dea82/FridgeAlarm/src/cont.c

/*
The MIT License (MIT)

Copyright (c) 2015-2016 Andreas L.

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
THE SOFTWARE IS PROVIDED "AS IS", WITHOUT WARRANTY OF ANY KIND, EXPRESS OR
IMPLIED, INCLUDING BUT NOT LIMITED TO THE WARRANTIES OF MERCHANTABILITY,
FITNESS FOR A PARTICULAR PURPOSE AND NONINFRINGEMENT. IN NO EVENT SHALL THE
AUTHORS OR COPYRIGHT HOLDERS BE LIABLE FOR ANY CLAIM, DAMAGES OR OTHER
LIABILITY, WHETHER IN AN ACTION OF CONTRACT, TORT OR OTHERWISE, ARISING FROM,
OUT OF OR IN CONNECTION WITH THE SOFTWARE OR THE USE OR OTHER DEALINGS IN
THE SOFTWARE.
*/

/**
 * @file
 */

#include "cont.h"

#include "butt.h"
#include "buzz.h"
#include "conf.h"
#include "ledc.h"
#include "door.h"
#include "pwrd.h"
#include "util.h"


typedef enum
{
    NO_CALIBRATION_E, CALIBRATION_SUCCESS_E, CALIBRATION_FAIL_E
} tCalibrationState_E;

static tCalibrationState_E getCalibrationState_E(void);
static void normalModeStateMachine(void);

void Cont_Init(void)
{
    /* Nothing */
}

void Cont_Loop(void)
{
    tCalibrationState_E calibrationState_E = getCalibrationState_E();

    /* Sets it default. */
    Pwrd_SetSleepMode(PWRD_SHORT_DEEP_SLEEP_E);

    if (calibrationState_E == CALIBRATION_SUCCESS_E)
    {
        Buzz_SetSound(BUZZ_OFF_E);
        Ledc_SetState(LEDC_GREEN_BLINK_E);
    }
    else if (calibrationState_E == CALIBRATION_FAIL_E)
    {
        Buzz_SetSound(BUZZ_ON_E);
        Ledc_SetState(LEDC_RED_BLINK_E);
        Pwrd_SetSleepMode(PWRD_SLEEP_WITH_TIMER_RUNNING_E);
    }
    else
    {
        normalModeStateMachine();
    }
}

static tCalibrationState_E getCalibrationState_E(void)
{
    static tCalibrationState_E calibrationState_E;
    tButt_State_str buttState_str = Butt_GetState_str();

    /* Calibration state */
    if ((buttState_str.state_E == BUTT_PRESSED_E) &&
        (buttState_str.tickInState_U08 * tick_U08c > calibrationTimeButton_U16c) &&
        (calibrationState_E == NO_CALIBRATION_E))
    {
        /* Enters calibration mode */
        if (Door_StoreClosedPos_B() == TRUE)
        {
            calibrationState_E = CALIBRATION_SUCCESS_E;
        }
        else
        {
            calibrationState_E = CALIBRATION_FAIL_E;
        }
    }
    else
    {
        /* Leaves calibration mode */
        if (buttState_str.state_E == BUTT_RELEASED_E)
        {
            calibrationState_E = NO_CALIBRATION_E;
        }
    }

    return calibrationState_E;
}

static void normalModeStateMachine(void)
{
    static tB inhibitAlarm_B;
    static tU08 counter_U08;
    tButt_State_str buttState_str = Butt_GetState_str();
    tDoor_State_str doorState_str = Door_GetState_str();

    if (doorState_str.position_E == DOOR_CLOSED_E)
    {
        Buzz_SetSound(BUZZ_OFF_E);
        if ((doorState_str.ticksInState_U16 > lightsOnDoorClosed_U16c / tick_U08c) &&
            (counter_U08 > minTimeAwake_U08c / tick_U08c) &&
            (buttState_str.state_E == BUTT_RELEASED_E))
        {
            /* When door has been closed for a long time and no activity
             * on button it's OK to go to deep sleep. */
            counter_U08 = 0;
            Ledc_SetState(LEDC_OFF_E);
            Pwrd_SetSleepMode(PWRD_LONG_DEEP_SLEEP_E);
        }
        else
        {
            /* Door has not been closed long enough to go to deep sleep. */
            Util_safeIncrementU08(&counter_U08);
            Ledc_SetState(LEDC_GREEN_E);
        }
        /* Reset */
        inhibitAlarm_B = FALSE;
    }
    else /* DOOR_OPEN_E */
    {
        counter_U08 = 0;

        if (doorState_str.ticksInState_U16 > alarmOpen_U16c / tick_U08c)
        {
            /* Door has been open too long, sound the alarm if button is not
             * inhibiting it from going off. */
            if (buttState_str.state_E == BUTT_PRESSED_E)
            {
                inhibitAlarm_B = TRUE;
            }
            if (inhibitAlarm_B == TRUE)
            {
                Buzz_SetSound(BUZZ_OFF_E);
            }
            else
            {
                Buzz_SetSound(BUZZ_ALARM_E);
                /* Necessary to have the timer running due to the buzzer. */
                Pwrd_SetSleepMode(PWRD_SLEEP_WITH_TIMER_RUNNING_E);
            }
            Ledc_SetState(LEDC_RED_BLINK_E);
        }
        else
        {
            /* Door open but not long enough to sound the alarm. */
            Ledc_SetState(LEDC_RED_E);
            Buzz_SetSound(BUZZ_OFF_E);
        }
    }
}
