dea82/FridgeAlarm/src/buzz.c

/*
The MIT License (MIT)

Copyright (c) 2015-2016 Andreas L.

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
THE SOFTWARE IS PROVIDED "AS IS", WITHOUT WARRANTY OF ANY KIND, EXPRESS OR
IMPLIED, INCLUDING BUT NOT LIMITED TO THE WARRANTIES OF MERCHANTABILITY,
FITNESS FOR A PARTICULAR PURPOSE AND NONINFRINGEMENT. IN NO EVENT SHALL THE
AUTHORS OR COPYRIGHT HOLDERS BE LIABLE FOR ANY CLAIM, DAMAGES OR OTHER
LIABILITY, WHETHER IN AN ACTION OF CONTRACT, TORT OR OTHERWISE, ARISING FROM,
OUT OF OR IN CONNECTION WITH THE SOFTWARE OR THE USE OR OTHER DEALINGS IN
THE SOFTWARE.
*/

/**
 * @file
 */

#include "buzz.h"

#include <avr/io.h>

#include "conf.h"
#include "type.h"

static const tU16 buzzAlarmPeriodTime_cU16 = 2000; /* [ms]*/
static const tU32 buzzerFreq_cU32 = 600; /* [Hz] */
#if defined(__AVR_ATtiny13A__)
/* Lower this for lower consumption and sound level. */
static const tU08 buzzerDutyCycle_cU08 = 10; /* [%] */
#endif

static tBuzz_SoundType_E soundType_E;

static void turnOn(void);
static void turnOff(void);

void Buzz_Init(void)
{
/* BuzzerFreq = F_CPU / (2 * Prescaler * (1 + OCR0A))
 *
 * In this case gives a buzzer frequency of 1690 Hz
 */
#if F_CPU == 8000000 && defined(__AVR_ATtiny85__)
    OCR0A = F_CPU / (buzzerFreq_cU32 * 64 * 2) - 1;
#elif F_CPU == 9600000 && defined(__AVR_ATtiny13A__)
    OCR0A = F_CPU / (buzzerFreq_cU32 * 64) - 1;
    OCR0B = (F_CPU / (buzzerFreq_cU32 * 64) - 1) * buzzerDutyCycle_cU08 / 100;
#else
#error "Buzzer module does not support this combination of MCU and clock frequency";
#endif
}

void Buzz_Loop(void)
{
    static tU08 counter_U08;

    if (soundType_E == BUZZ_ON_E)
    {
        turnOn();
        counter_U08 = 0;
    }
    else if (soundType_E == BUZZ_ALARM_E)
    {
        if (++counter_U08 > buzzAlarmPeriodTime_cU16 / tick_U08c)
        {
            counter_U08 = 0;
        }
        if (counter_U08 < buzzAlarmPeriodTime_cU16 / (tick_U08c / HALF_DIVISOR))
        {
            turnOn();
        }
        else
        {
            turnOff();
        }
    }
    else
    {
        turnOff();
        counter_U08 = 0;
    }
}

static void turnOn(void)
{
    /* Enable module before accessing registers */
    PRR = PRR_INIT & ~_BV(PRTIM0);
#if defined(__AVR_ATtiny85__)
    /* Set to 'CTC' mode, toggle on match */
    TCCR0A = _BV(COM0A0) | _BV(WGM01);
    /* Start clock - prescaler 64 */
    TCCR0B = _BV(CS01) | _BV(CS00);
#elif defined(__AVR_ATtiny13A__)
    /* Set to fast PWM mode, 50% duty cycle */
    TCCR0A = _BV(COM0B1) | _BV(WGM01) | _BV(WGM00);
    /* Start clock - prescaler 64 */
    TCCR0B = _BV(WGM02) | _BV(CS01) | _BV(CS00);
#else
#error "Buzz module does not support this MCU."
#endif


}

static void turnOff(void)
{
    /* Stop clock */
    TCCR0B = 0;
    /* Normal port operation, disconnect OC0A with potential of leaving
     * pin state high. */
    TCCR0A = 0;
    /* Disconnect module */
    PRR = PRR_INIT | _BV(PRTIM0);
}

void Buzz_SetSound(const tBuzz_SoundType_E soundTypeReq_E)
{
    soundType_E = soundTypeReq_E;
}
