dea82/FridgeAlarm/src/tools/piezo-tester/main.c

#include <avr/io.h>
#include <util/delay.h>

/* Declaring main as OS_main saves some register pushing to stack. */
int main(void) __attribute__((OS_main));
int main(void)
{

#if F_CPU == 9600000
    OCR0A = 86;
    OCR0B = 43;
#else
#error "Correct compare value to CPU speed."
#endif

DDRB = _BV(PB1);

    for(;;)
    {
        /* Set to 'CTC' mode, toggle on match */
        TCCR0A = _BV(COM0B1) | _BV(WGM01) | _BV(WGM00);
        /* Start clock - prescaler 64 */
        TCCR0B = _BV(WGM02) | _BV(CS01) | _BV(CS00);
        _delay_ms(3000);

        TCCR0B = 0;
        TCCR0A = 0;
        _delay_ms(1000);
    }
}
